DRAMCO/Plant-Sensor/V2/Hardware/Renders/plant_sensor_v2_back.png

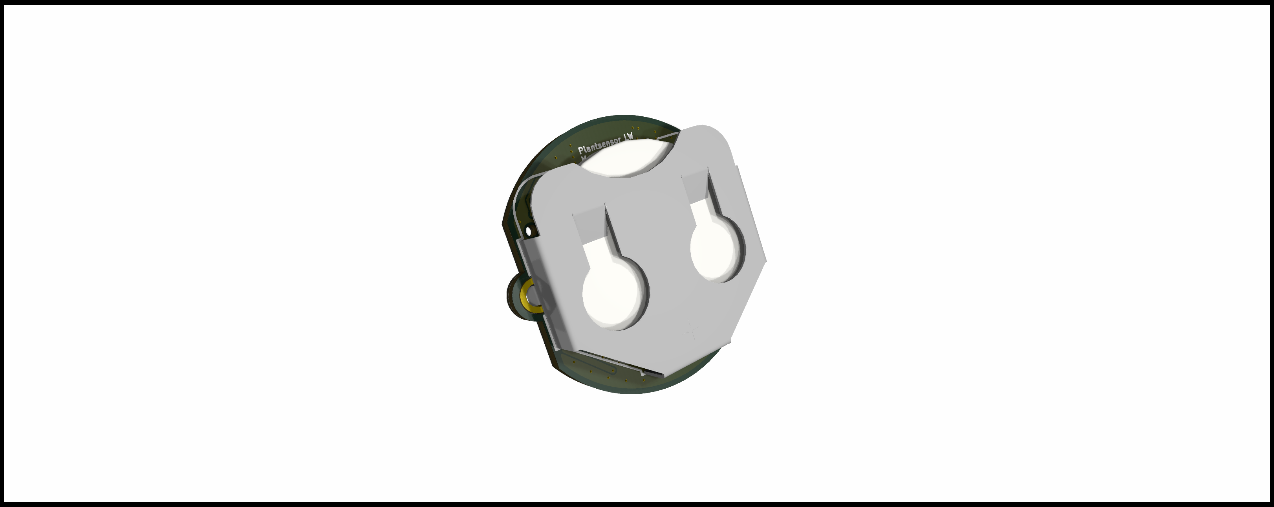
V2/Hardware/Renders/plant_sensor_v2_back.png
