DRAMCO/Plant-Sensor/V2/Software/BLE_Beacon/Core/Src/stm32wb0x_hal_msp.c

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

/* Includes ------------------------------------------------------------------*/
#include "main.h"
/* USER CODE BEGIN PFP */
static void lowPowerIOSetup(void);
/* USER CODE END PFP */

/* External functions --------------------------------------------------------*/
/**
  * Initializes the Global MSP.
  */
void HAL_MspInit(void)
{

  /* USER CODE BEGIN MspInit 0 */

  /* IOs configuration to have the lowest power consumption in DEEPSTOP */
  lowPowerIOSetup();

  /* USER CODE END MspInit 0 */

  __HAL_RCC_SYSCFG_CLK_ENABLE();

  /* System interrupt init*/

}

/* USER CODE BEGIN 1 */

/**
  * @brief  Configures the IOs pull resistors to have the optimized power consumption.
  * @param  None
  * @retval None
  */
static void lowPowerIOSetup(void)
{
  
  HAL_PWREx_EnableGPIOPullUp(PWR_GPIO_A, 
                       PWR_GPIO_BIT_0|
                       PWR_GPIO_BIT_1|
                       PWR_GPIO_BIT_2|                         
                       PWR_GPIO_BIT_3);
  
  HAL_PWREx_EnableGPIOPullDown(PWR_GPIO_A, 
                             PWR_GPIO_BIT_8|
                             PWR_GPIO_BIT_9|
                             PWR_GPIO_BIT_10|
                             PWR_GPIO_BIT_11);
  
  HAL_PWREx_EnableGPIOPullDown(PWR_GPIO_B, 
                             PWR_GPIO_BIT_0|
                             PWR_GPIO_BIT_3|
                             PWR_GPIO_BIT_6|
                             PWR_GPIO_BIT_7|
                             PWR_GPIO_BIT_12|
                             PWR_GPIO_BIT_13);
  
  HAL_PWREx_EnableGPIOPullUp(PWR_GPIO_B, 
                       PWR_GPIO_BIT_1|
                       PWR_GPIO_BIT_2|
                       PWR_GPIO_BIT_4|
                       PWR_GPIO_BIT_5|  
                       PWR_GPIO_BIT_14|
                       PWR_GPIO_BIT_15);
}

/* USER CODE END 1 */
