DRAMCO/Plant-Sensor/V2/Software/test/Core/Src/main.c

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
/* Includes ------------------------------------------------------------------*/
#include "main.h"


static uint32_t delay = 250;
ADC_HandleTypeDef hadc4;

CRC_HandleTypeDef hcrc;

RAMCFG_HandleTypeDef hramcfg_SRAM1;

RNG_HandleTypeDef hrng;

RTC_HandleTypeDef hrtc;

TIM_HandleTypeDef htim16;

UART_HandleTypeDef huart1;
DMA_HandleTypeDef handle_GPDMA1_Channel1;
DMA_HandleTypeDef handle_GPDMA1_Channel0;

void SystemClock_Config(void);
void PeriphCommonClock_Config(void);
static void MX_GPIO_Init(void);
static void MX_GPDMA1_Init(void);
/**
  * @brief  The application entry point.
  * @retval int
  */
int main(void)
{

  /* MCU Configuration--------------------------------------------------------*/

  /* Reset of all peripherals, Initializes the Flash interface and the Systick. */
  HAL_Init();
  /* Config code for STM32_WPAN (HSE Tuning must be done before system clock configuration) */
  MX_APPE_Config();

  /* Configure the system clock */
  SystemClock_Config();

  /* Configure the peripherals common clocks */
  PeriphCommonClock_Config();

  /* Initialize all configured peripherals */
  MX_GPIO_Init();
  MX_GPDMA1_Init();
  MX_ADC4_Init();
  MX_CRC_Init();
  MX_ICACHE_Init();
  MX_RAMCFG_Init();
  MX_RNG_Init();
  MX_RTC_Init();
  MX_TIM16_Init();
  /* Initialize leds */
  BSP_LED_Init(LED_BLUE);
  BSP_LED_Init(LED_GREEN);
  BSP_LED_Init(LED_RED);

  /* Initialize USER push-button, will be used to trigger an interrupt each time it's pressed.*/
  BSP_PB_Init(B1, BUTTON_MODE_EXTI);
  BSP_PB_Init(B2, BUTTON_MODE_EXTI);
  BSP_PB_Init(B3, BUTTON_MODE_EXTI);

  /* USER CODE BEGIN BSP */

  /* -- Sample board code to switch on leds ---- */
  BSP_LED_On(LED_BLUE);
  BSP_LED_On(LED_GREEN);
  BSP_LED_On(LED_RED);

  /* USER CODE END BSP */

  /* Init code for STM32_WPAN */
  MX_APPE_Init(NULL);

  /* Infinite loop */
  /* USER CODE BEGIN WHILE */
  while (1)
  {

    /* -- Sample board code for User push-button in interrupt mode ---- */
    BSP_LED_Toggle(LED_BLUE);
    HAL_Delay(delay);

    BSP_LED_Toggle(LED_GREEN);
    HAL_Delay(delay);

    BSP_LED_Toggle(LED_RED);
    HAL_Delay(delay);

    /* USER CODE END WHILE */
    MX_APPE_Process();

    /* USER CODE BEGIN 3 */
  }
  /* USER CODE END 3 */
}

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
/**
  * @brief EXTI line detection callback.
  * @param GPIO_Pin: Specifies the pins connected EXTI line
  * @retval None
  */
void HAL_GPIO_EXTI_Falling_Callback(uint16_t GPIO_Pin)
{
  switch(GPIO_Pin)
  {
    case B1_PIN:
      /* Change the period to 100 ms */
      delay = 100;
      break;
    case B2_PIN:
      /* Change the period to 500 ms */
      delay = 500;
      break;
    case B3_PIN:
      /* Change the period to 1000 ms */
      delay = 1000;
      break;
    default:
      break;
  }
}

/**
  * @brief  This function is executed in case of error occurrence.
  * @retval None
  */
void Error_Handler(void)
{
  /* USER CODE BEGIN Error_Handler_Debug */
  /* User can add his own implementation to report the HAL error return state */
  __disable_irq();
  while (1)
  {
  }
  /* USER CODE END Error_Handler_Debug */
}

#ifdef  USE_FULL_ASSERT
/**
  * @brief  Reports the name of the source file and the source line number
  *         where the assert_param error has occurred.
  * @param  file: pointer to the source file name
  * @param  line: assert_param error line source number
  * @retval None
  */
void assert_failed(uint8_t *file, uint32_t line)
{
  /* USER CODE BEGIN 6 */
  /* User can add his own implementation to report the file name and line number,
     ex: printf("Wrong parameters value: file %s on line %d\r\n", file, line) */
  /* USER CODE END 6 */
}
#endif /* USE_FULL_ASSERT */
